psu-epl/lid-button/Pictures/FinishedBottom.jpg

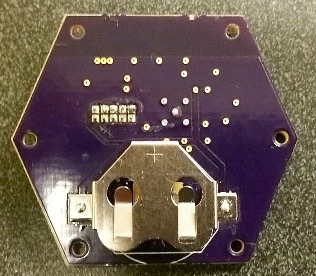
Pictures/FinishedBottom.jpg
