psu-epl/lid-button/Pictures/FinishedTop.jpg

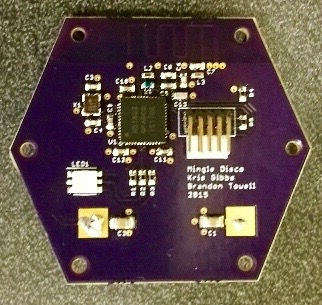
Pictures/FinishedTop.jpg
