psu-epl/lid-button/Pictures/HexCaseBottom.jpg

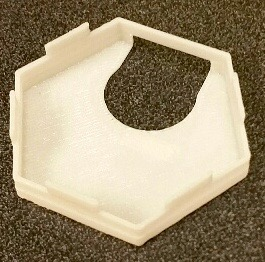
Pictures/HexCaseBottom.jpg
