psu-epl/lid-button/Pictures/HexCaseTop.jpg

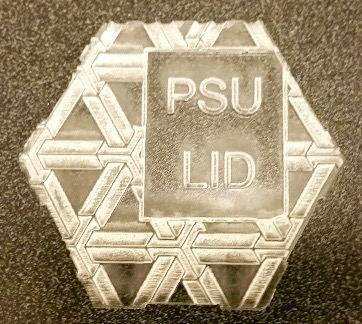
Pictures/HexCaseTop.jpg
