psu-epl/lid-button/Pictures/MultiMeter.jpg

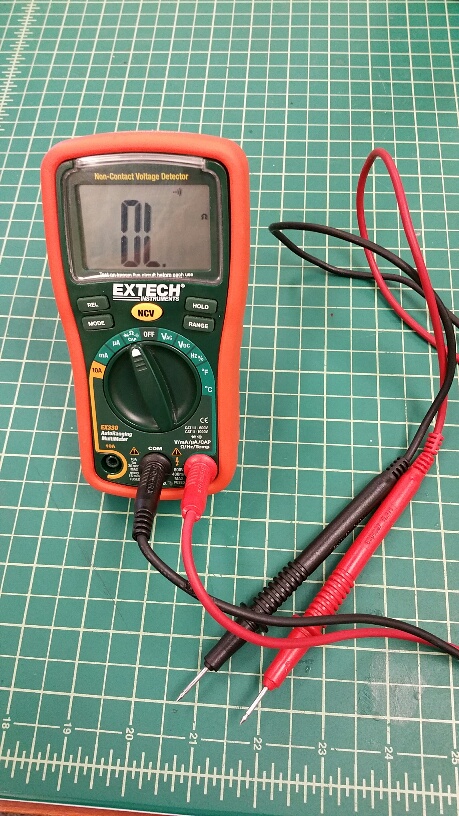
Pictures/MultiMeter.jpg
