psu-epl/lid-button/Pictures/PluggedInBoard.jpg

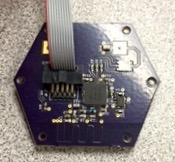
Pictures/PluggedInBoard.jpg
