psu-epl/lid-button/Pictures/PowerOn.jpg

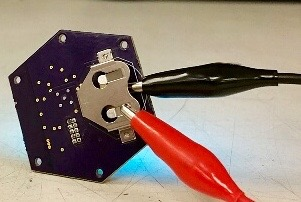
Pictures/PowerOn.jpg
