psu-epl/lid-button/Pictures/PowerSetUp.jpg

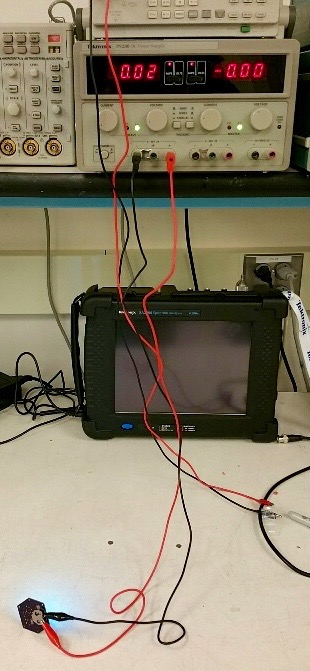
Pictures/PowerSetUp.jpg
