psu-epl/lid-button/Pictures/RoutedBottom.jpg

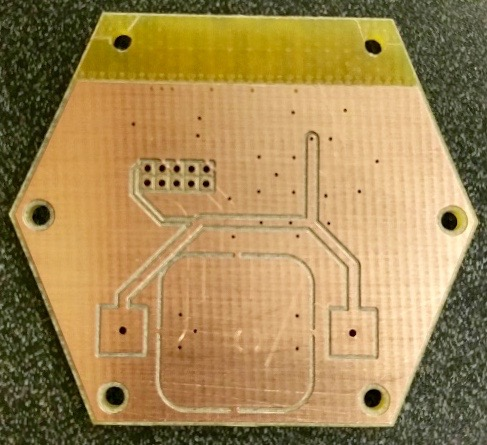
Pictures/RoutedBottom.jpg
