psu-epl/lid-button/Pictures/RoutedTop.jpg

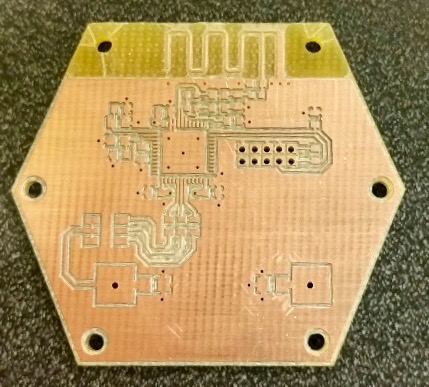
Pictures/RoutedTop.jpg
