psu-epl/lid-button/Pictures/Us.jpg

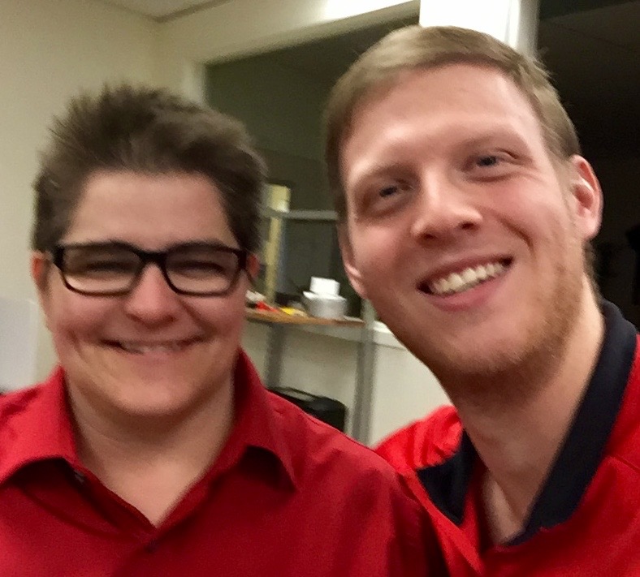
Pictures/Us.jpg
