psu-epl/lid-button/Documentation/Debug out header.tiff

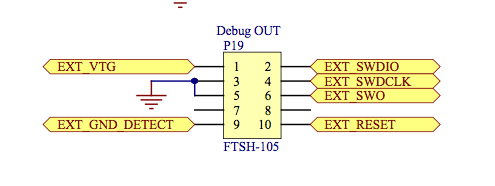
Documentation/Debug out header.tiff
